dh219/ST_HD_Emulator/emu.h

/*
 * ATARI ST HDC Emulator
 * 
 * File:    emu.h
 * Author:  Steve Bradford
 * Created: September 2022
 *
 * ACSI-AHDI Command Set
 * ref: Atari ACSI/DMA Integration Guide - June 28, 1991
 * 

    Atari ACSI DMA pinout, looking at the male connector at the ATARI computer:
             19 pin D-SUB
    ---------------------------------
    \ 01 02 03 04 05 06 07 08 09 10 /
     \ 11 12 13 14 15 16 17 18 19  /
       ---------------------------
Pin	Name	Description
1	D0	Data 0
2	D1	Data 1
3	D2	Data 2
4	D3	Data 3
5	D4	Data 4
6	D5	Data 5
7	D6	Data 6
8	D7	Data 7
9	_CS	Chip Select
10	IRQ	Interrupt Request
11	GND	Ground
12	/RST	Reset
13	GND	Ground
14	ACK	Acknowledge           
15	GND	Ground
16	A1	Address bit
17	GND	Ground
18	R/W	Read/Write
19	_DRQ    Data Request

// ATARI Document Archive https://docs.dev-docs.org/
// in category: "Hard Drive" Application Notes on the Atari Computer System Interface (ACSI) [Sep 27 1985]
//
// +++++++++++++++++++++++++++++++++++++++++++++++++++++++++++++++++++++++
// ----- Command Phase ---------------------------------------------------
// DATA direction: From Atari to Target Device                          
// A1    ¯¯¯¯¯¯¯¯\___________________________/¯¯¯¯¯¯¯¯¯¯¯¯¯¯¯¯¯¯¯¯¯¯¯¯¯¯ LOW indicates 1st byte of new command.
// IRQ   ¯¯¯¯¯¯¯¯¯¯¯¯¯¯¯¯¯¯¯¯¯¯¯¯¯¯¯¯¯\___________/¯¯¯¯¯¯¯¯¯¯¯¯¯¯¯\_____ Active low driven by target device to indicate (A) readness to accept another command byte (B) the availability of a byte to be read.
// _CS   ¯¯¯¯¯¯¯¯¯¯¯¯¯\__________/¯¯¯¯¯¯¯¯¯¯¯¯¯¯¯¯\__________/¯¯¯¯¯¯¯¯¯¯
//                     |        |                  |        |           
// R/_W  ¯¯¯¯¯¯\______________________/¯¯¯¯¯¯\____________________/¯¯¯¯¯ LOW from ATARI to Device (Write), HIGH from Device to ATARI (Read)
//               |     |        |     |      |     |        |     |     
// DATA  =======><-------VALID--------><====><-------VALID--------><==== 8bit DATA Bus
//               |     |        |     |      |     |        |     |     
//               |<-a->|<--b--->|<-c->|      |<-a->|<--b--->|<-c->|     
//                Byte 0                      Byte 1                     Byte n
// Timing
// a)  60 ns  (max)
// b)  250 ns (max)
// c)  20 ns  (max)
// IRQ Active LOW (open-collector) 1K Pullup on ATARI.
//
// +++++++++++++++++++++++++++++++++++++++++++++++++++++++++++++++++++++++
// ----- Status Phase ----------------------------------------------------
// DATA direction: From Target Device to Atari     
// A1    ¯¯¯¯¯¯¯¯¯¯¯¯¯¯¯¯¯¯¯¯¯¯¯¯¯¯¯¯¯¯¯¯¯¯¯¯¯¯¯¯¯¯ HIGH indicates inactive.
// IRQ   ______________/¯¯¯¯¯¯¯¯¯¯¯¯¯¯¯¯¯¯¯¯¯¯¯¯¯¯¯ Active LOW driven by target device to indicate (A) readness to accept another command byte (B) the availability of a byte to be read.
// _CS   ¯¯¯¯¯¯¯¯¯¯¯¯¯¯\_______________/¯¯¯¯¯¯¯¯¯¯¯
//                     |              |            
// R/_W  _______/¯¯¯¯¯¯¯¯¯¯¯¯¯¯¯¯¯¯¯¯¯¯¯¯¯¯¯¯\_____ LOW from ATARI to Device (Write), HIGH from Device to ATARI (Read)
//              |      |              |      |     
// DATA  =====================><----VALID----><==== 8bit DATA Bus
//              |      |              |      |     
//              |<-a-->|<--b-->|<-c-->|<-d-->|     
//                              Byte 0             
// Timing
// a)  50 ns  (max)
// b)  150 ns (max)
// c)  100 ns (max)
// d)  80 ns  (max)
//
// +++++++++++++++++++++++++++++++++++++++++++++++++++++++++++++++++++++++
// ----- DMA - Data Out Phase --------------------------------------------
// DATA direction: From Atari to Target Device      
// A1   : ¯¯¯¯¯¯¯¯¯¯¯¯¯¯¯¯¯¯¯¯¯¯¯¯¯¯¯¯¯¯¯¯¯¯¯¯¯¯¯¯¯¯ HIGH indicates inactive.
// DRQ  : ¯¯¯¯¯¯¯\_______________/¯¯¯¯¯¯¯¯¯¯¯¯¯¯\___ Active LOW, DMA Device Data request, Used by the peripheral to request a DMA data transfer.
//                 |                                
// _ACK : ¯¯¯¯¯¯¯¯¯¯¯¯¯¯¯\______________/¯¯¯¯¯¯¯¯¯¯¯
// R/_W :          |     |      ?       |     |      LOW from ATARI to Device (Write), HIGH from Device to ATARI (Read)
//                 |     |              |     |     
// DATA   ========><----------VALID-----------><==== 8bit DATA Bus
//                 |     |              |     |     
//                 |<-a->|<-----b------>|<-a->|     
//               |<--c-->|              |<--d-->|   
// Timing
// a)  60 ns  (max)
// b)  250 ns (max)
// c)  240 ns (max)
// d)  240 ns (min)
// DRQ Active LOW (open-collector) 1K Pullup on ATARI.
//
// +++++++++++++++++++++++++++++++++++++++++++++++++++++++++++++++++++++++
// ----- DMA - Data In Phase ---------------------------------------------
// DATA direction: From Target Device to Atari      
// A1   : ¯¯¯¯¯¯¯¯¯¯¯¯¯¯¯¯¯¯¯¯¯¯¯¯¯¯¯¯¯¯¯¯¯¯¯¯¯¯¯¯¯¯ HIGH indicates inactive.
// DRQ  : ¯¯¯¯¯¯\________________/¯¯¯¯¯¯¯¯¯¯¯¯¯¯¯¯¯¯ Active LOW, DMA Device Data request, Used by the peripheral to request a DMA data transfer.
//                |                                 
// _ACK : ¯¯¯¯¯¯¯¯¯¯¯¯¯¯¯\______________/¯¯¯¯¯¯¯¯¯¯¯
//                |     ||              |           
// DATA   =============><--------VALID--------><==== 8bit DATA Bus
//                |     ||              |     |     
//                |<-a->||<-----b------>|<-c->|     
// Timing
// a)  60 ns  (max)
// b)  250 ns (max)
// c)  50 ns  (min)
// DRQ Active LOW (open-collector) 1K Pullup on ATARI.
 * 
 *
 *
 * 
 * Hardware configuration
 * 
 * 
 * GPIO 00 - 29 are available to the programmer
 * GPIO 16, 17, 18, 19 reserved for SPI0
 * GPIO 23, 25 are not to be used because of board design
 * 
 * SPI0 assignments
 * 16   SPI0_Rx   MISO (Master In Slave Out)
 * 17   SPI0_CS
 * 18   SPI0_CLK
 * 19   SPI0_Tx   MOSI (Master Out Slave In)
 * 
 * GPIO assignments
 * 00   Data bit 0              BIDIRECTIONAL
 * 01   Data bit 1              BIDIRECTIONAL
 * 02   Data bit 2              BIDIRECTIONAL
 * 03   Data bit 3              BIDIRECTIONAL
 * 04   Data bit 4              BIDIRECTIONAL
 * 05   Data bit 5              BIDIRECTIONAL
 * 06   Data bit 6              BIDIRECTIONAL
 * 07   Data bit 7              BIDIRECTIONAL
 * 08   /CS                     INPUT
 * 09   /IRQ                    OUTPUT
 * 10   /RST                    INPUT
 * 11   /ACK                    INPUT
 * 12   A1                      INPUT
 * 13   R/W                     INPUT
 * 14   /DRQ                    OUTPUT
 * 15   /Interface Enable       OUTPUT          control tri-state octal driver chip on the data bus - low to enable
 *                                      
 *                                              NOTE - Hardware design - tie the DIR pin on the tri-state buffer to the RW signal
 *                                                     meaning GPIO 20 will not be needed
 * 16
 * 17   microSD card 1 CS       OUTPUT
 * 18
 * 19
 * 20   microSD card 2 CS       OUTPUT
 */

#ifndef _EMU_H
#define _EMU_H

#include "pico.h"
#include <stdbool.h>
#include "hardware/spi.h"
#include "hardware/sync.h"
#include "sdcard/sd_card.h"
#include "emuscsi.h"


/* build options */
#define DEBUG               1                   /* enable debug stuff */
#define ICD_RTC             0                   /* include ICD RTC - will only be used if ICD driver is used */
#define DEBUG_ICDRTC        0                   /* ICD RTC debug */
#define USEDMA              1                   /* use DMA transfers for SPI - sdcard/spi.h also needs this define */
#define PROJECT_HARDWARE    0                   /* set when using project hardware  0 = PROTOTYPE */
#define PICO_W              0                   /* set when running on a Raspberry PI PICO-W OOOOOO what could be coming ??? */
#define WRITE_ENABLE        1                   /* 0 disable writes if debugging problems */
#define DEBUG_IO            0

/* GPIO assignments by GPIO number */
#define D0                  0                   /* GPIO 00-07 bi-directional */
#define CS                  8                   /* GPIO 08 input  */
#define IRQ                 9                   /* GPIO 09 output */
#define RST                 10                  /* GPIO 10 input  */
#define ACK                 11                  /* GPIO 11 input  */
#define A1                  12                  /* GPIO 12 input  */
#define RW                  13                  /* GPIO 13 input  - read active-high, write active-low */
#define DRQ                 14                  /* GPIO 14 output */
#define DATA_BUS_CNTRL      15                  /* GPIO 15 output - data bus control - low = high-impedance */
#define SPI_SDO             16                  /* GPIO 16 output - MISO */
#define MICROSD_CARD_CS0    17                  /* GPIO 17 output - microSD card socket 1 CS, active-low */
#define SPI_CLK             18                  /* GPIO 18 output - microSD SPI clock */
#define SPI_SDI             19                  /* GPIO 19 input  - MOSI */
#define MICROSD_CARD_CS1    20                  /* GPIO 20 output - microSD card socket 2 CS, active-low */
#define MICROSD_CARD_CD0    21                  /* GPIO 21 input  - microSD card socket 1 CD, active-low */
#define MICROSD_CARD_CD1    22                  /* GPIO 22 input  - microSD card socket 2 CD, active-low */
#if PICO_W
#define ONBOARD_LED         WL_GPIO0            /* WLGPIO 0 output - onboard LED */
#else
#define ONBOARD_LED         25                  /* GPIO 25 output - PI PICO onboard LED */
#endif
#define CONTROLLER_SELECT   26                  /* GPIO 26 input  - hardware controller ID match - high = selected */
#define RTC_ENABLED         27                  /* GPIO 27 input  - hardware jumper 5-6 ON = high = RTC enabled */
#define CONTROL_BUS_CNTRL   28                  /* GPIO 28 output - control bus enable */

/* ACSI BUS signals */
#define DATA_MASK           (1 << D0)           /* 0x00000000 */
#define CS_MASK             (1 << CS)           /* 0x00000100 */
#define IRQ_MASK            (1 << IRQ)          /* 0x00000200 */
#define RST_MASK            (1 << RST)          /* 0x00000400 */ 
#define ACK_MASK            (1 << ACK)          /* 0x00000800 */ 
#define A1_MASK             (1 << A1)           /* 0x00001000 */ 
#define RW_MASK             (1 << RW)           /* 0x00002000 */ 
#define DRQ_MASK            (1 << DRQ)          /* 0x00004000 */ 

/* GPIO output masks - 32 bit values */
#define SPI_CS0_MASK        (1 << MICROSD_CARD_CS0) /* 0x00020000 */
#define SPI_CS1_MASK        (1 << MICROSD_CARD_CS1) /* 0x00100000 */
#define SPI_CS_MASK         (SPI_CS0_MASK | SPI_CS1_MASK) 
#define LED_MASK            (1 << ONBOARD_LED)      /* 0x02000000 */
#define DATA_BUS_CNTRL_MASK (1 << DATA_BUS_CNTRL)   /* 0x00008000 */
#define ACSI_DATA_MASK      0x000000ff          /* bits 0 - 7  ACSI bus data bits */
#define ACSI_CNTRL_MASK     0x00007f00          /* bits 8 - 14 ACSI bus control bits */
#define GPIO_MASK           0x1e7fffff          /* all gpio pins used for this project */
#define CONTROL_BUS_CNTRL_MASK (1 << CONTROL_BUS_CNTRL)  /* GPIO 28 output - control bus enable */

/* set 1 for each GPIO as an output */  
#define GPIO_OUTPUTS_MASK   ((uint32_t)(DRQ_MASK | SPI_CS_MASK | IRQ_MASK | LED_MASK | DATA_BUS_CNTRL_MASK | CONTROL_BUS_CNTRL_MASK ))



/* Emulator configuration */
#define CONTROLLER_ID       0                   /* we identify as this ID - MAX ID 6 */
                                                /* NOTE the hardware is limited to setting IDs 0-3 only */
                                                /* ID + 1 is assigned though eg. select ID 3, ID3 AND ID4 will be used */
#define TARGET0             CONTROLLER_ID       /* Hard Drive Emulator Controller Address 1st SD card */
#define TARGET1             (CONTROLLER_ID + 1) /* Hard Drive Emulator Controller Address 2nd SD card */
#define TARGET6             6                   /* ICD RTC  - we use this ID if hardware RTC is enabled */
#define MAX_DRIVES          2                   /* physical constraints mean we can only have 2 micro-sd cards */
#define MAX_ID              7                   /* 7 should never be used - reserved for the host ie. the ATARI PC */
#define MAX_MBR_PARTS       4                   /* */
#define MAX_LUNS            8                   /* max of 8 logical units per controller */

#define LO                  0                   /* signal level, 0v */
#define HI                  1                   /* signal level, vcc */

                                                /* 74lvc245 chips need OE low whilst the txb0108 chips need OE high */
#if PROJECT_HARDWARE
#define ENABLE              1                   /* enable bidirectional voltage level translator chip */
#define DISABLE             0                   /* disable bidirectional voltage level translator chip - tristate */
#else
#define ENABLE              0                   /* enable bidirectional voltage level translator chip */
#define DISABLE             1                   /* disable bidirectional voltage level translator chip - tristate */
#endif

                                                /* 1.0  Initial release                                                    */
                                                /* 1.1  altered for multiple sd-cards                                      */
                                                /* 1.2  additional shell commands                                          */
                                                /* 1.3  fixed target id + spi config changes                               */
                                                /* 1.4  two sd cards now functional + additional cpdisk shell command      */
                                                /* 1.41 added extra GPIO for RTC enable - ICD driver only (ID6)            */
                                                /* 1.5  sd-card optimisations - added local sdcard and spi interface files */
                                                /* 1.51 code optimisations all over and code tidy-up                       */
                                                /* 1.52 added GPIO 28 to enable control bus                                */
                                                /* 1.6  ICD RTC emulation added                                            */
                                                /* 1.61 fixed disk mount problem                                           */
                                                /* 1.7  HW design problems. Can not use TXB0108 part */
#define VERSION             "1.7"              /* major.minor max length 4 */
#define TITLE               "\n\033[2J" \
                            "********************************\n" \
                            "BBaN RPP HDC\n" \
                            "ATARI ACSI HDC Emulator\n" \
                            __DATE__"  "__TIME__\
                            "\nBuild "\
                            VERSION\
                            "   Steve Bradford\n" \
                            "********************************\n"

#define IRQ_LO()            gpio_put (IRQ, LO);
#define IRQ_HI()            gpio_put (IRQ, HI);
#define DRQ_LO()            gpio_put (DRQ, LO);
#define DRQ_HI()            gpio_put (DRQ, HI);

#define dataBus(s)          gpio_put (DATA_BUS_CNTRL, s)
#define controlBus(s)       gpio_put (CONTROL_BUS_CNTRL, s)

#if PROJECT_HARDWARE
#define newCMD()            (gpio_get (A1) == LO && gpio_get (RW) == LO)
//#define newCMD()            (gpio_get (CONTROLLER_SELECT) == HI)

#else
#define newCMD()            (gpio_get (A1) == LO && gpio_get (RW) == LO)
#endif

#define rdDataBus()         (gpio_get_all () & ACSI_DATA_MASK)
#define wrDataBus(d)        gpio_put_masked ( ACSI_DATA_MASK, (d) )
#define checkRST()          {                               \
                                if ( gpio_get (RST) == LO ) \
                                    gotRST = true;          \
                            }
#define checkCS()           while ( gpio_get ( CS  ) == LO )
#define waitCS()            while ( gpio_get ( CS  ) == HI )
#define waitRW(s)           while ( gpio_get ( RW  ) == s  )
#define waitACK(s)          while ( gpio_get ( ACK ) == s  )
#define waitRD()            while ( gpio_get ( RW  ) == LO )
#define waitWR()            while ( gpio_get ( RW  ) == HI )
#define waitA1()            while ( gpio_get ( A1  ) == LO )
#define waitRST()           while ( gpio_get ( RST ) == LO )

#define usDelay(x)          {                                           \
                                uint64_t tick = time_us_64 () + (x);    \
                                while ( time_us_64 () < tick );         \
                            }

#define Nop()               asm volatile ("nop\n")

#define FREAD               true
#define FWRITE              false

#define MHZ                 1000000

#if USEDMA
 extern volatile uint32_t intState;

 #define enableInterrupts()  ; //(restore_interrupts (intState))
 #define disableInterrupts() ; //(intState = save_and_disable_interrupts ())
#else
 #define enableInterrupts() ;
 #define disableInterrupts() ;
#endif


/* 
 * disk drive structures 
 *
 * drives are the sd-cards
 * luns are the partitions
 * e.g. 
 * drive 0, partition 3 = sdcard 0, lun 2
 * drive 1, partition 1 = sdcard 1, lun 0
 * 
 */

typedef struct DRIVE_INFO 
{    
    bool      writeProtected;                   /* true = write protected */

    uint8_t   status;                           /* drive current status */
    uint8_t   lastStatus;
    //bool      mounted;                          /* true = drive mounted */
    //bool      raw;                              /* true = a partioned micro-sd card, false = FAT32 *.img files */
    bool      ejected;                          /* true = disk eject command issued */
    bool      prevState;                        /* false = inserted, true = removed */
    bool      locked;                           /* prevent / allow media removal - true = locked (prevent) */
    
    scsiStatus_t lastError;                     /* SCSI 24 bit error code */
    uint32_t     lba;                           /* logical block address passed in by the command */
    uint32_t     len;                           /* data length for extended SCSI commands */

    //uint8_t   partTotal;                        /* partitions on drive */
    
    sd_card_t *pSD;
    uint32_t  packetCount;                      /* keep a tally of the command count for drive - just for stats */
    uint32_t  diskSize;                         /* disk size - number of 512 byte sectors */

} 
DRIVES;


extern int      mountRAW        ( int );
extern bool     sd_init_driver  ();
extern int      sd_init_card    ( sd_card_t *);
extern int      sd_write_blocks ( sd_card_t *, const uint8_t *, uint64_t, uint32_t);
extern int      sd_read_blocks  ( sd_card_t *, uint8_t *, uint64_t, uint32_t);
extern bool     sd_card_detect  ( sd_card_t *);
extern uint64_t sd_sectors      ( sd_card_t *);
extern void     modeSense0      ( char *, DRIVES *, int );
extern void     modeSense4      ( char *, DRIVES *, int );
extern void     checkSDcards    ( void );


extern sd_card_t sd_cards [];

#endif
