dh219/ST_HD_Emulator/shell/emushell.h

/* 
 * ATARI ST HDC Emulator
 *
 * File:    emushell.h
 * Author:  Steve Bradford
 * Created: 1st Nov 2022
 * 
 * Shell header file
 * 
 */

#ifndef _EMU_SHELL_H
#define _EMU_SHELL_H

#define GOOD                    false
#define BAD                     true

#define NOT                     !

#define MAXCFGLINES             10
#define MAX_ARGS                5
#define MAX_ARG_LENGTH          40

#define SHELL_CMDBUF            80                                              /* CP/M command line buffer size */

#define SYNTAX( command )       printf( "\t%s: Syntax error\n", command );

#define BS                      0x08
#define DEL                     0x7f
#define CR                      0x0d
#define LF                      0x0a
#define ESC                     0x1b
#define SPACE                   0x20


/* psh declarations */
int  chgdisk ( int, char* );
void doShell (void );


/* external functions */
extern bool emudate     (char*, bool);
extern bool format      (char);
extern void help        (char*);
//extern bool mount       (int, char*, int);
extern void psh         (void);
extern bool quit        (void);
extern bool reboot      (void);
extern bool rmdisk      (char*);
extern bool status      (void);
extern bool emutime     (char*, bool);
extern bool umount      (int, int);
extern bool uptime      (void);
extern bool cpuFreq     (char* );
extern bool status      (void);
extern void emumount    (int);
extern void emuunmount  (int);
extern bool cpdisk      (char*, char*);
extern void debugVerbose (char*);
extern bool sdtest      (char*);

/* external variables */



#endif
